OPRobots/FujitoraBot/src/src/debug.c

#include "debug.h"

bool debug_enabled = false;
uint32_t last_print_debug = 0;

#define LOG_SIZE 1000
#define LOG_FIELDS 2
#define LOG_INTERVAL 1
uint32_t last_log_millis = 0;
uint16_t arr_log_index = 0;

int32_t arr_log[LOG_SIZE][LOG_FIELDS];

/**
 * @brief Imprime los valores de los sensores sin aplicar ninguna corrección
 *
 */
static void debug_sensors_raw(void) {
  if (get_clock_ticks() > last_print_debug + 50) {

    for (int8_t sensor = get_sensors_line_num() - 1; sensor >= 0; sensor--) {
      printf("%d\t", get_sensor_raw(sensor));
    }

    if (get_config_robot() == CONFIG_ROBOT_ROBOTRACER) {
      printf("\t");
      for (int8_t sensor = get_sensors_line_num(); sensor < get_sensors_num(); sensor++) {
        printf("%d\t", get_sensor_raw(sensor));
      }
    }
    printf("\n");
    last_print_debug = get_clock_ticks();
  }
}

/**
 * @brief Imprime los valores de los sensores calibrándolos y escalandolos
 *
 */
static void debug_sensors_calibrated(void) {
  if (get_clock_ticks() > last_print_debug + 50) {
    for (int8_t sensor = get_sensors_line_num() - 1; sensor >= 0; sensor--) {
      printf("%d\t", get_sensor_calibrated(sensor));
    }

    if (get_config_robot() == CONFIG_ROBOT_ROBOTRACER) {
      printf("\t");
      for (int8_t sensor = get_sensors_line_num(); sensor < get_sensors_num(); sensor++) {
        printf("%d\t", get_sensor_calibrated(sensor));
      }
    }
    printf("\n");
    last_print_debug = get_clock_ticks();
  }
}

static void debug_all_leds(void) {
  set_RGB_rainbow();
  set_neon_heartbeat();
  warning_status_led(125);
}

static void debug_digital_io(void) {
  if (get_clock_ticks() > last_print_debug + 250) {
    printf("BTN: %d SW1: %d SW2: %d SW3: %d CFM: %d CFU: %d CFD: %d\n", get_start_btn(), get_swtich_1(), get_swtich_2(), get_swtich_3(), get_menu_mode_btn(), get_menu_up_btn(), get_menu_down_btn());
    last_print_debug = get_clock_ticks();
  }
}

static void debug_posicion_correccion(void) {
  if (get_clock_ticks() > last_print_debug + 50) {

    calc_sensor_line_position();
    float correccion_velocidad = calc_pid_correction(get_sensor_line_position());

    printf("%.3f - %ld\n", correccion_velocidad, get_sensor_line_position());
    last_print_debug = get_clock_ticks();
  }
}

static void debug_line_position(void) {
  if (get_clock_ticks() > last_print_debug + 50) {
    calc_sensor_line_position();
    printf("%d\t%ld\t%d\n", -(get_sensors_line_num() + 2) * 1000 / 2, get_sensor_line_position(), (get_sensors_line_num() + 2) * 1000 / 2);
    last_print_debug = get_clock_ticks();
  }
}

static void debug_encoders(void) {
  if (get_clock_ticks() > last_print_debug + 50) {
    printf("%ld (%ld)\t%ld (%ld)\n", get_encoder_left_total_ticks(), get_encoder_left_micrometers(), get_encoder_right_total_ticks(), get_encoder_right_micrometers());
    last_print_debug = get_clock_ticks();
  }
}

static void debug_motors(void) {
  if (is_esc_inited()) {
    set_motors_speed(15, 15);
  }
}

static void debug_fans(void) {
  if (is_esc_inited()) {
    if (get_config_robot() == CONFIG_ROBOT_LINEFOLLOWER) {
      set_fan_speed(70);
    } else {
      set_fans_speed(50, 50);
    }
  }
}

static void check_debug_btn(void) {
  if (get_start_btn()) {
    debug_enabled = !debug_enabled;
    while (get_start_btn()) {
    }
    delay(50);
  }
  if (debug_enabled) {
    set_neon_heartbeat();
  } else {
    set_neon_fade(0);
  }
}

void debug_from_config(uint8_t type) {
  check_debug_btn();
  if (debug_enabled) {
    switch (type) {
      case DEBUG_TYPE_SENSORS_RAW:
        debug_sensors_raw();
        break;
      case DEBUG_TYPE_SENSORS_CALIBRATED:
        debug_sensors_calibrated();
        break;
      case DEBUG_TYPE_LINE_POSITION:
        debug_line_position();
        break;
      case DEBUG_TYPE_MOTORS:
        debug_motors();
        break;
      case DEBUG_TYPE_ENCODERS:
        debug_encoders();
        break;
      case DEBUG_TYPE_DIGITAL_IO:
        debug_digital_io();
        break;
      case DEBUG_TYPE_CORRECCION_POSICION:
        debug_posicion_correccion();
        break;
      case DEBUG_TYPE_LEDS_PARTY:
        debug_all_leds();
        break;
      case DEBUG_TYPE_FANS_DEMO:
        debug_fans();
        break;
    }
  } else {
    switch (type) {
      case DEBUG_TYPE_MOTORS:
        set_motors_speed(0, 0);
        break;
      case DEBUG_TYPE_LEDS_PARTY:
        all_leds_clear();
        break;
      case DEBUG_TYPE_FANS_DEMO:
        set_fan_speed(0);
        break;
    }
  }
}

void debug_sensors_calibration(void) {
  if (get_clock_ticks() > last_print_debug + 1000) {
    print_sensors_calibrations();
    last_print_debug = get_clock_ticks();
  }
}

void update_log(void) {
  if (get_clock_ticks() > last_log_millis + LOG_INTERVAL) {
    if (arr_log_index >= LOG_SIZE - 1) {
      for (uint16_t i = 0; i < LOG_SIZE - 1; i++) {
        for (uint16_t j = 0; j < LOG_FIELDS - 1; j++) {
          arr_log[i][j] = arr_log[i + 1][j];
        }
      }
    }

    arr_log[arr_log_index][0] = get_sensor_line_position();
    arr_log[arr_log_index][1] = get_encoder_avg_speed() * 100;

    if (arr_log_index < LOG_SIZE - 1) {
      arr_log_index++;
    }
    last_log_millis = get_clock_ticks();
  }
}

void debug_log(void) {
  printf("%s;%s;%s\n", "time", "line_position", "avg_speed_ms");
  for (uint16_t i = 0; i <= arr_log_index; i++) {
    printf("%d;%ld;%ld\n", i * LOG_INTERVAL, arr_log[i][0], arr_log[i][1]);
  }
}
